Cypherock/emfi-board/images/DUT_ATSAMD51J20A-AU.png

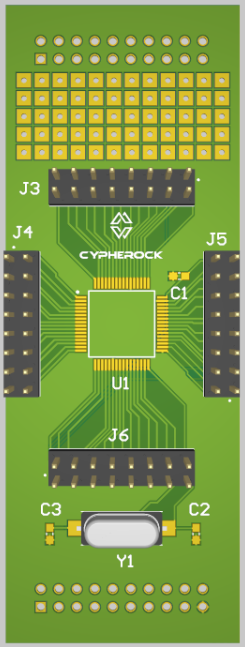
images/DUT_ATSAMD51J20A-AU.png
