Cypherock/emfi-board/images/DUT_ESP32-D0WD-V3.png

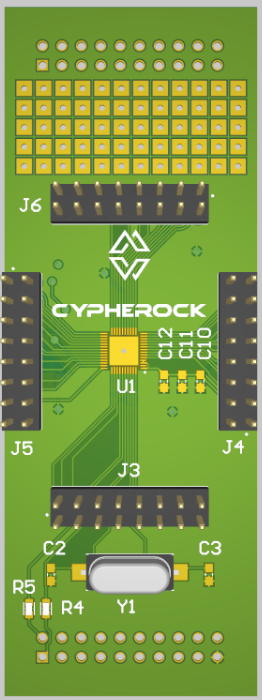
images/DUT_ESP32-D0WD-V3.png
