Cypherock/emfi-board/images/DUT_STM32F205RET6.png

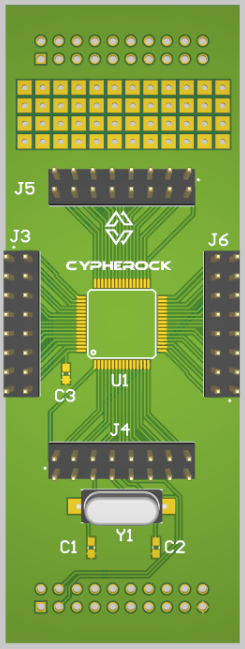
images/DUT_STM32F205RET6.png
